AugustoS97/cessna-switch-panel/cessna-panel-pcb/3D Model/cessna-panel-pcb.png

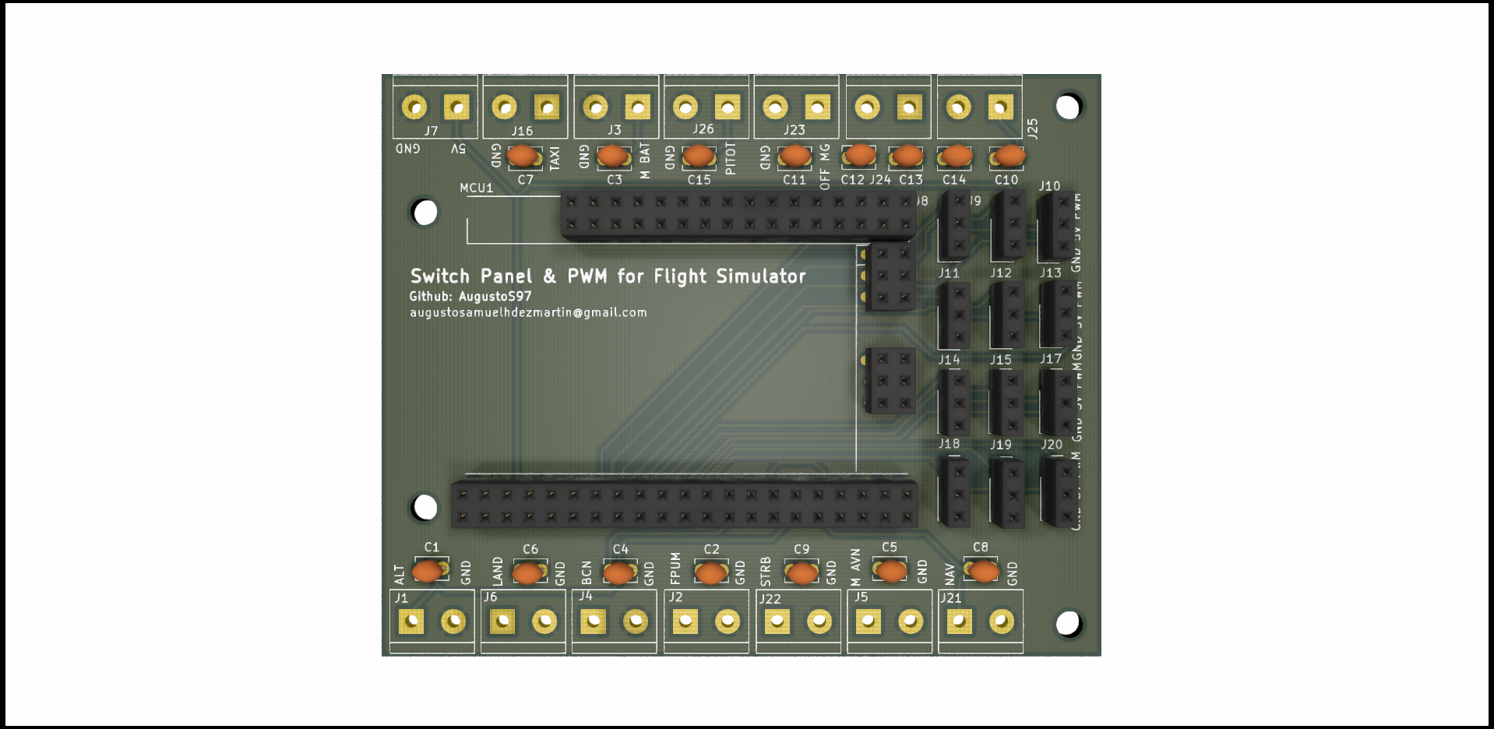
cessna-panel-pcb/3D Model/cessna-panel-pcb.png
