AugustoS97/cessna-switch-panel/cessna-panel-pcb/3D Model/Render-cessna-panel-pcb-1.png

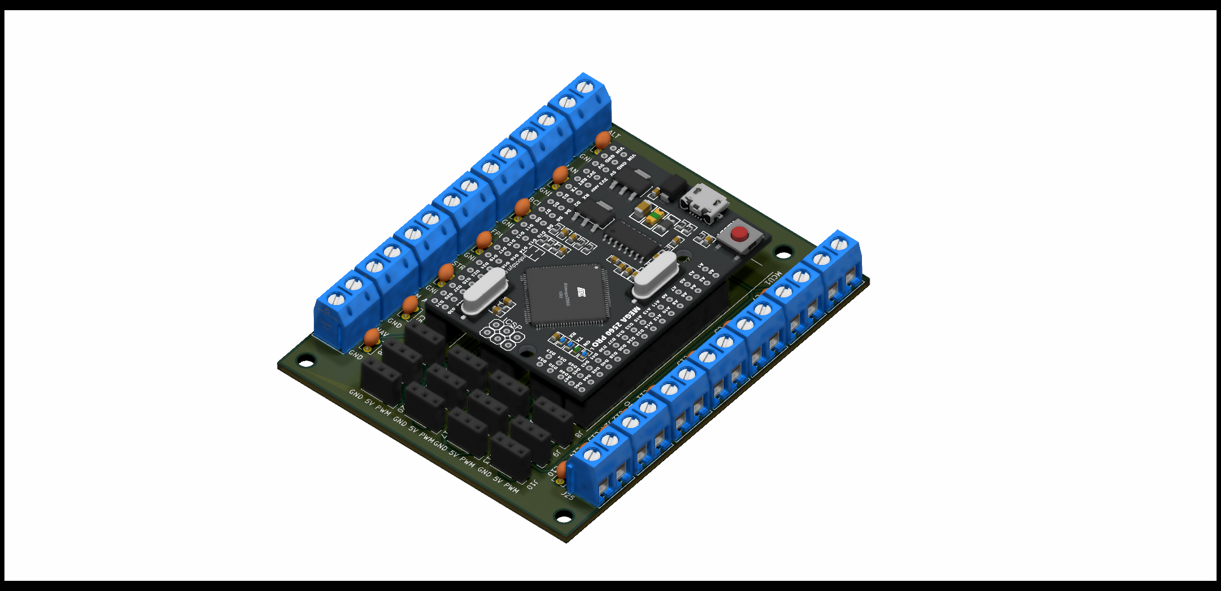
cessna-panel-pcb/3D Model/Render-cessna-panel-pcb-1.png
