AugustoS97/cessna-switch-panel/Frame-design/Photos/compress/IMG_20220708_230558.jpg

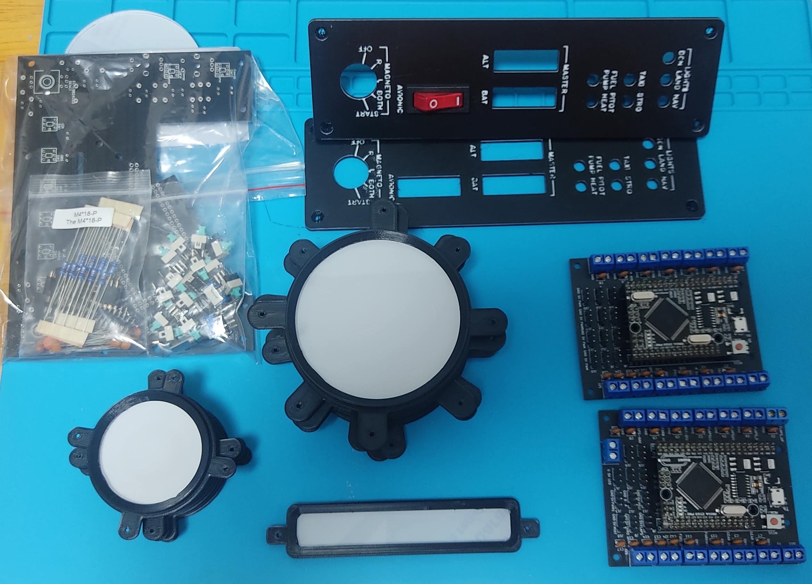
Frame-design/Photos/compress/IMG_20220708_230558.jpg
