AugustoS97/cessna-switch-panel/Frame-design/Photos/compress/IMG_20220812_184137.jpg

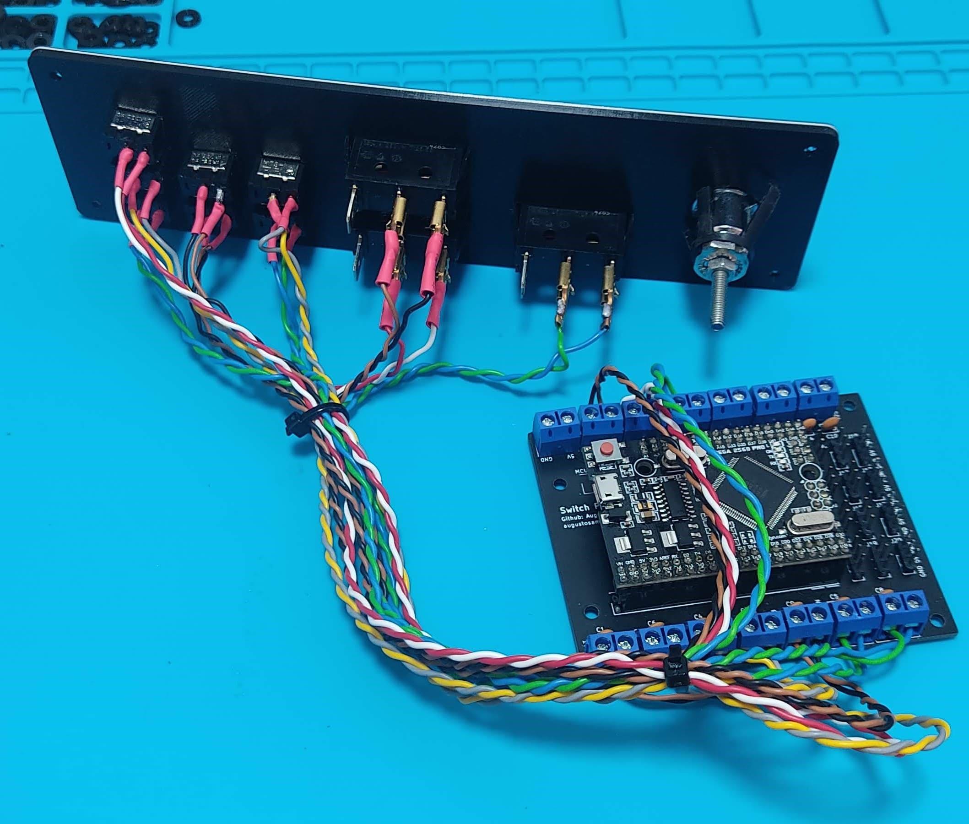
Frame-design/Photos/compress/IMG_20220812_184137.jpg
