AugustoS97/cessna-switch-panel/PCB-Support/IMAGES/compress/Foto pieza impresa.jpg

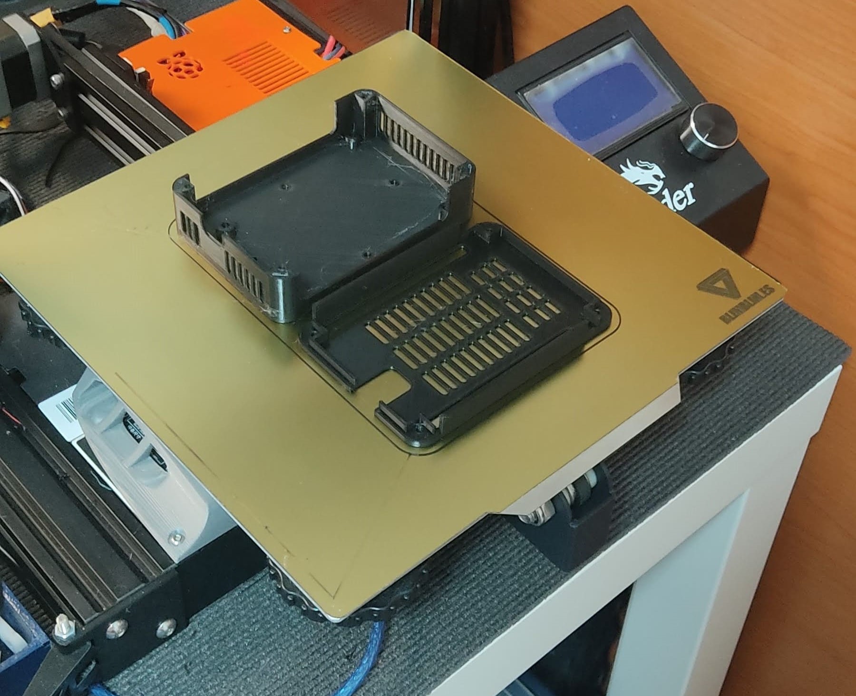
PCB-Support/IMAGES/compress/Foto pieza impresa.jpg
