AugustoS97/cessna-switch-panel/PCB-Support/IMAGES/compress/PCB.jpg

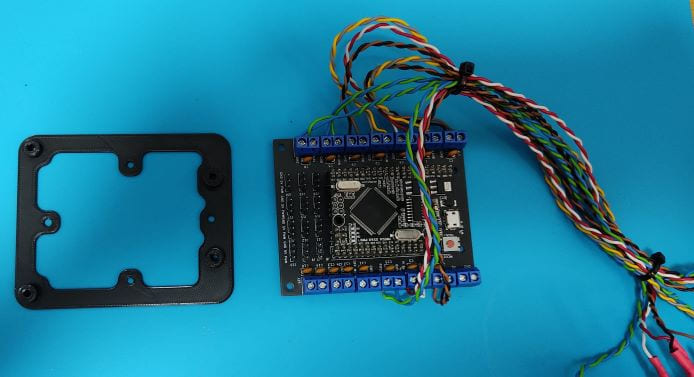
PCB-Support/IMAGES/compress/PCB.jpg
