AugustoS97/cessna-switch-panel/PCB-Support/IMAGES/compress/Soporte PCB Switch sin tapa v6.png

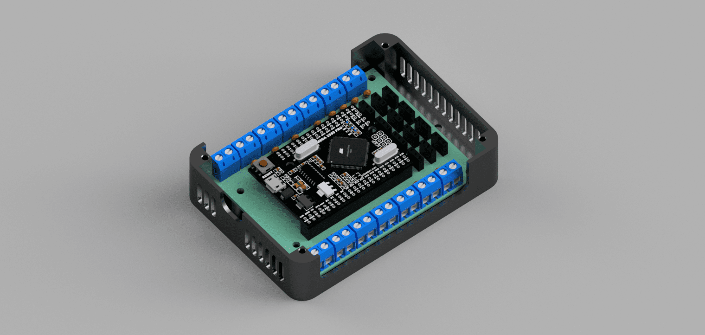
PCB-Support/IMAGES/compress/Soporte PCB Switch sin tapa v6.png
