AugustoS97/cessna-switch-panel/PCB-Support/IMAGES/Foto pieza impresa.jpg

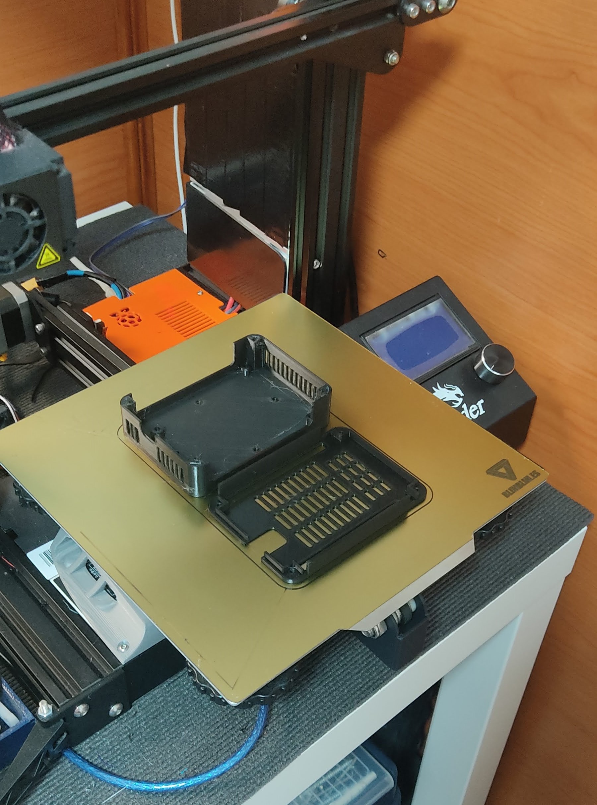
PCB-Support/IMAGES/Foto pieza impresa.jpg
