AugustoS97/cessna-switch-panel/PCB-Support/IMAGES/PCB.jpg

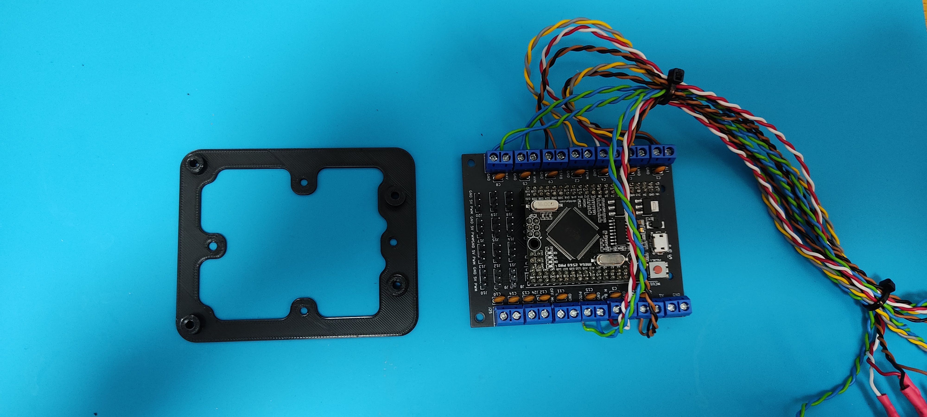
PCB-Support/IMAGES/PCB.jpg
